MauroMoreyra/EquipoAVL_pcb/TrackerAVL/doc/kicad/Kicad-Multicapa.pdf

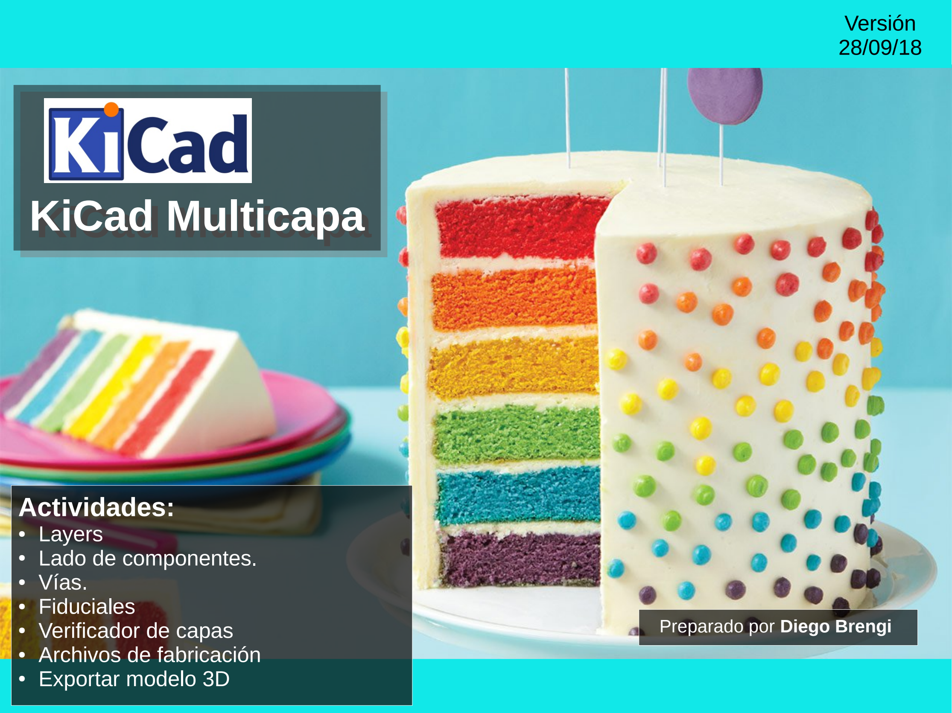
[picture p43: page 1]

# KiCad Multicapa

Preparado por Diego Brengi

Versión
28/09/18

### Actividades:

- Layers
- Lado de componentes.
- Vías.
- Fiduciales
- Verificador de capas
- Archivos de fabricación
- Exportar modelo 3D

Kicad Multicapa – Diego Brengi

Tomaremos el esquemático del ejercicio del oscilador y reharemos el PCB con las siguientes pautas:
- Con componentes SMD.
- Utilizando 4 capas.
- Con componentes de ambos lados.

### Ejercicio Multicapa

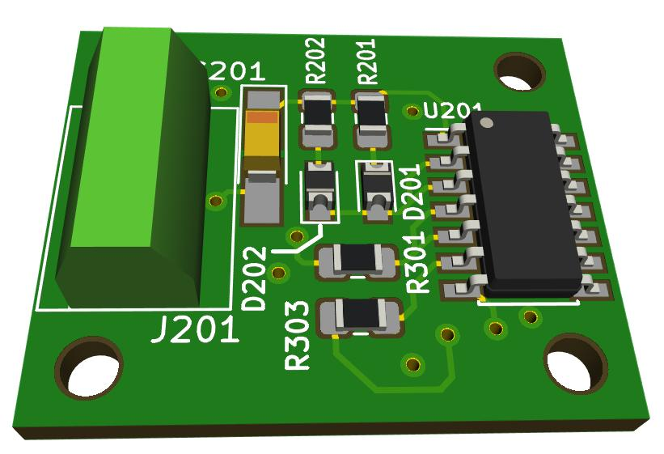
[picture p44: figure]

# CVPCB

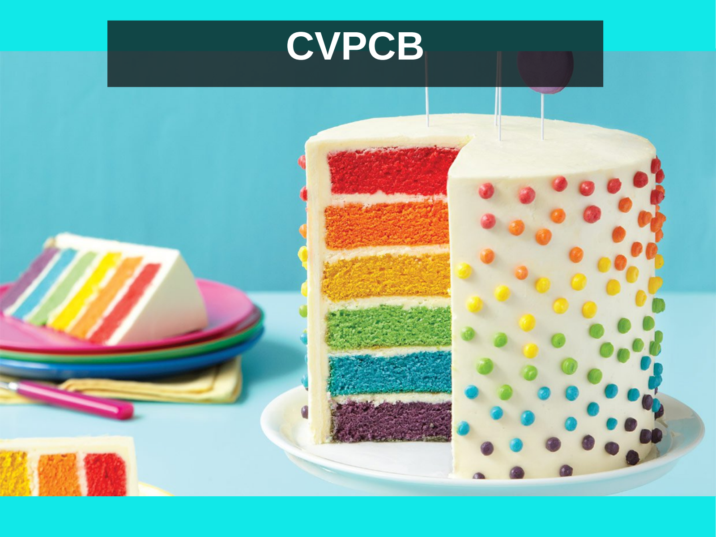
[picture p45: page 3]

Realizamos la asociación de lo componentes, que serán todos SMD salvo la bornera de alimentación.

### Asociación de huellas

Usaremos encapsulados 0805

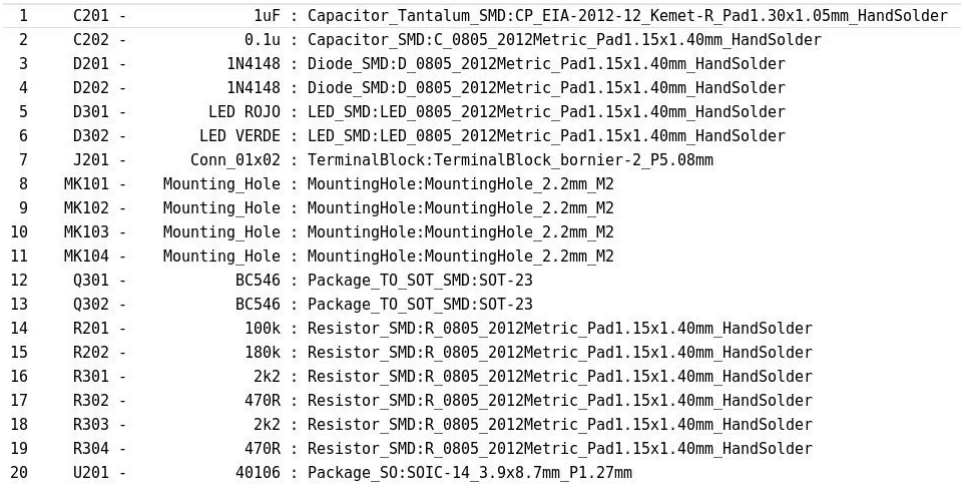
[picture p46: figure]

# PCBNEW

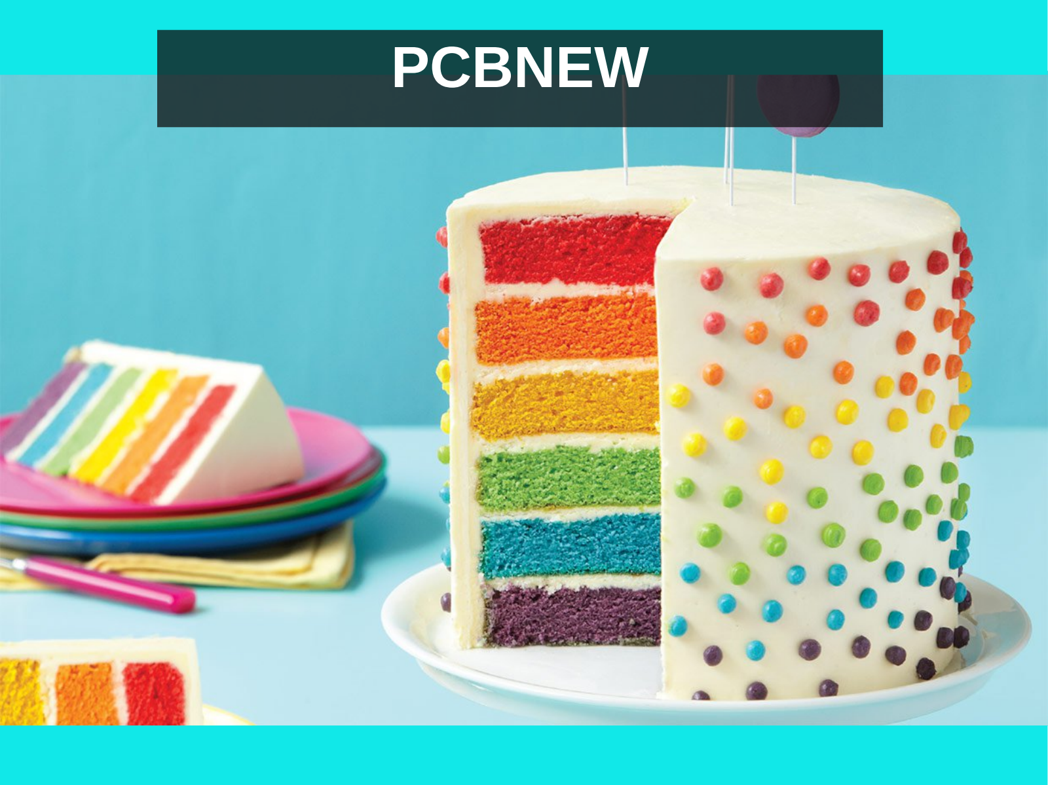
[picture p47: page 5]

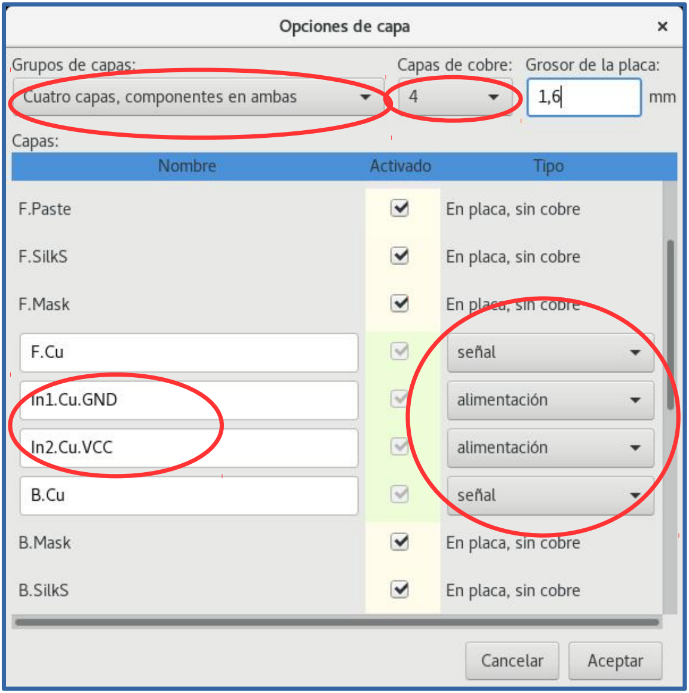
[picture p48: figure]

### Configurar:

- Número de capas.
- Componentes en ambas capas.
- Tipo de capas.
- Nombres de las capas.

### Configurar capas

Utilizaremos un plano completo para GND y otro para VCC.

### Componentes de ambos lados

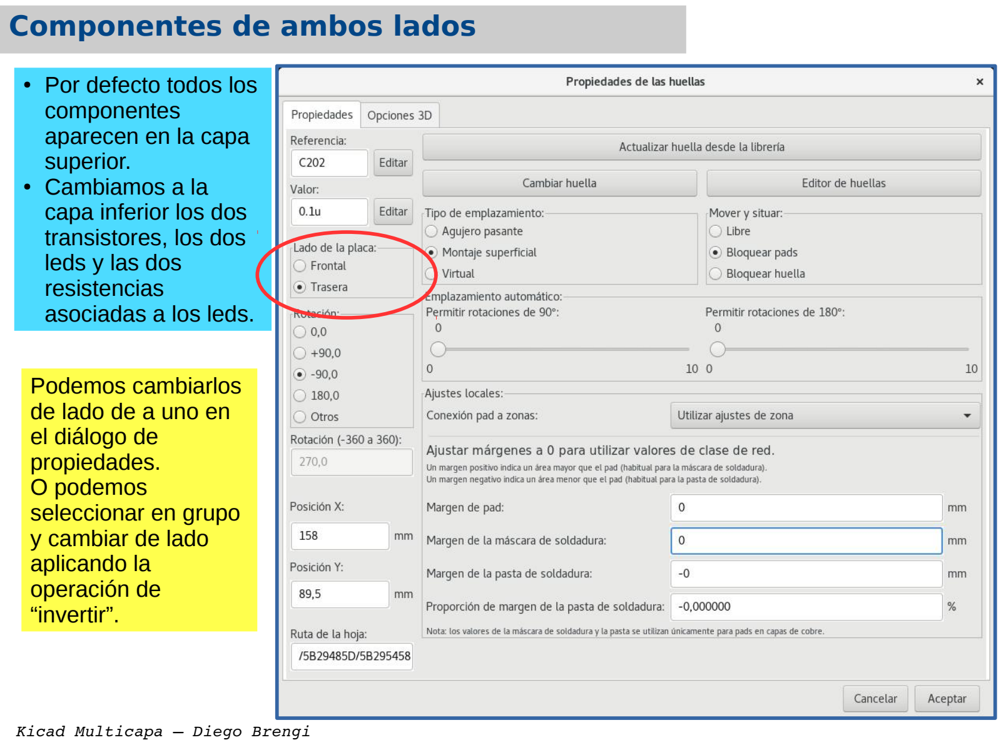
[picture p49: page 7]

- Por defecto todos los
componentes
aparecen en la capa
superior.
- Cambiamos a la
capa inferior los dos
transistores, los dos
leds y las dos
resistencias
asociadas a los leds.

Podemos cambiarlos
de lado de a uno en
el diálogo de
propiedades.
O podemos
seleccionar en grupo
y cambiar de lado
aplicando la
operación de
“invertir”.

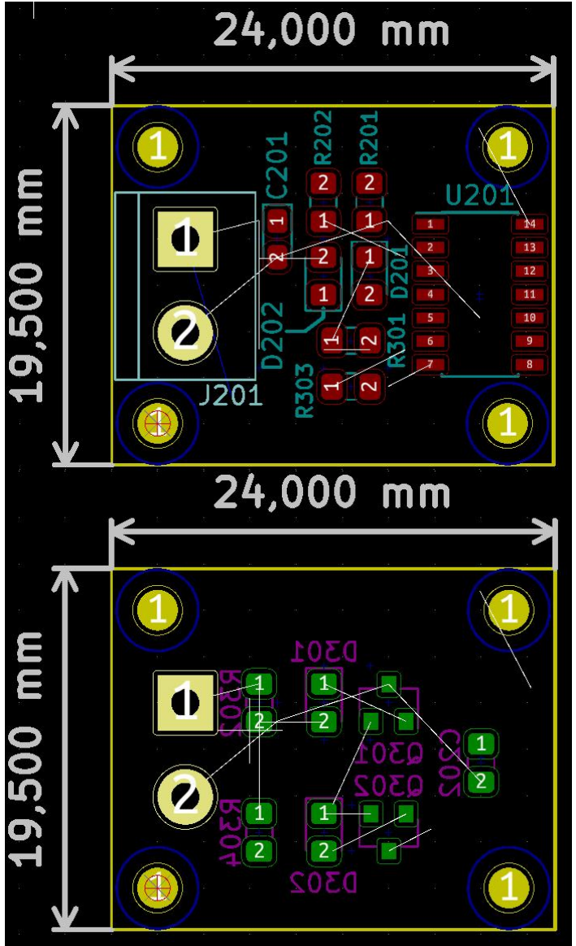
[picture p50: figure]

- Colocar una grilla adecuada.
- Se recomienda 0,5 mm o 0,25 mm.

### Grilla, borde, y ubicación

- Trazar el borde de PCB, de aprox. 24X20 mm.
- Ubicar los componentes.

Tomar las pautas de 10 mils de Mayer:
- Configurar vías: 1mm/0,5mm
- Configurar márgen: 0,25 mm
- Mínima pista: 0,25 mm
- Distancia al borde: 0,3 mm.

- Dibujar los rellenos de cobre, usando toda la capa 2 para GND y toda la 3 para VCC (+5V).

### Planos internos (GND y VCC)

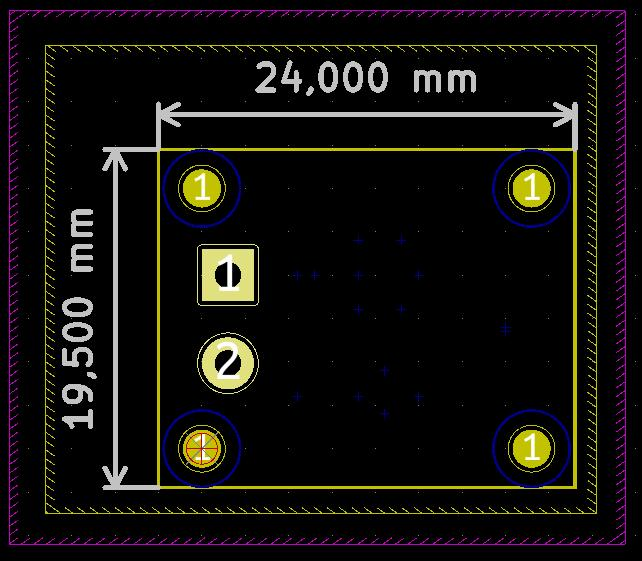
[picture p51: figure]

- Si ya estamos seguros de la ubicación de los componentes, podemos
conectar las alimentaciones a sus correspondientes planos.
Conexiónes de alimentación | La conexión se realizará con una pista corta y una vía.

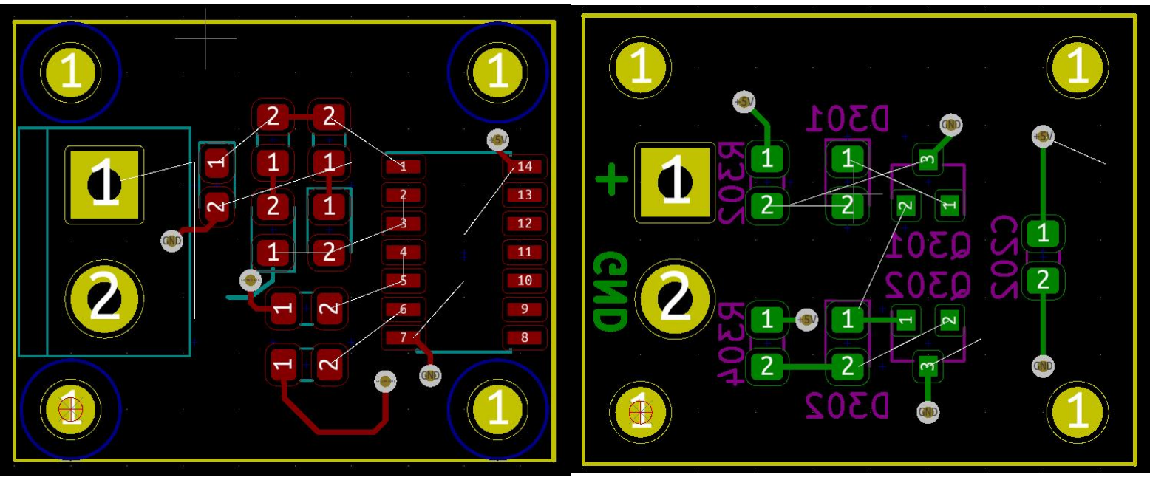
[picture p52: figure]

- Rutear el resto de las conexiones, en capa superior e inferior según corresponda.

### Ruteo de señal

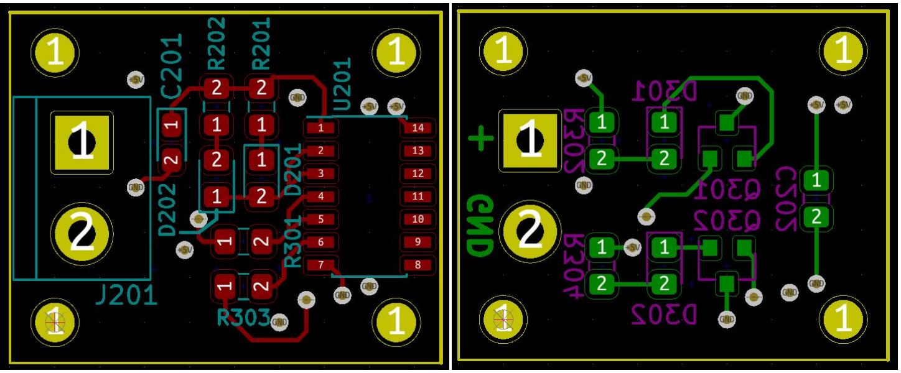
[picture p53: figure]

- Acomodamos las referencias en la serigrafía.
- Agregamos textos en la serigrafía de ambas caras.
- Agregamos IND. ARG. O INDUSTRIA ARGENTINA en alguna capa exterior de cobre.
- Al texto de IND. ARG le quitamos la máscara antisoldante.

### Serigrafía

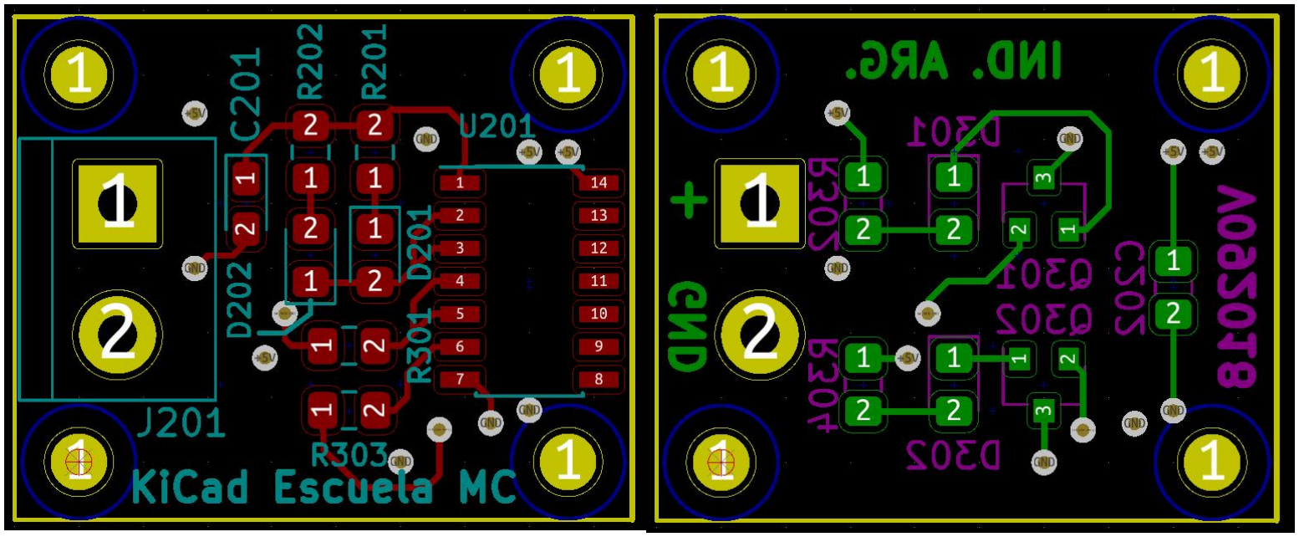
[picture p54: figure]

Agregamos un fiducial en cada capa, aunque lo ideal sería agregar dos o tres por capa para facilitar la tarea del armador.

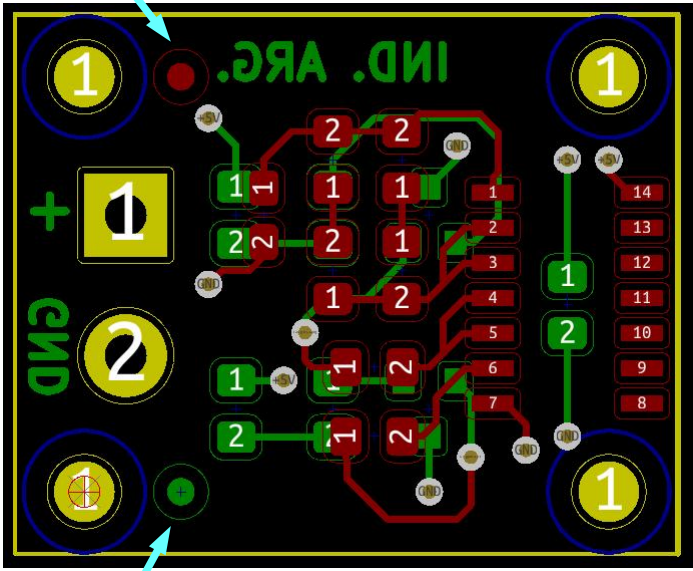
[picture p55: figure]

- Lo hacemos desde el
esquemático.
- Si no encontramos un
símbolo para el Fiducial
podemos usar el símbolo de Mounting Hole, renombrando la referencia a Fx (F1 y F2).
- Luego le asignamos con
CVPCB un fiducial de 1mm
de diámetro interno y 2 mm de diámetro externo.
- En el editor de PCB,
colocamos un fiducial en la capa de cobre superior y el otro en la capa de cobre
inferior.

### Fiduciales

### Verificador de capas

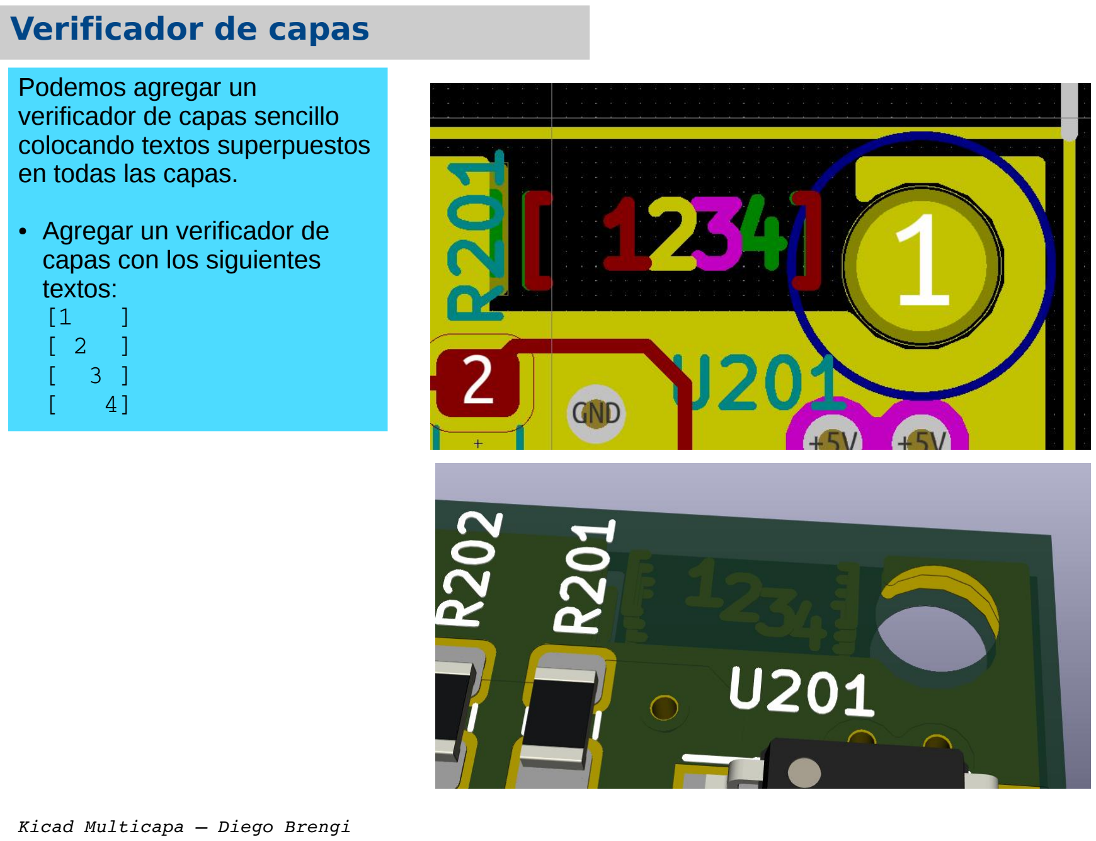
[picture p56: page 14]

Podemos agregar un
verificador de capas sencillo colocando textos superpuestos en todas las capas.
- Agregar un verificador de capas con los siguientes
textos:
[1 ]
[ 2 ]
[ 3 ]
[ 4]

- Realizar Chequeo de DRC y Listado de no conectados.
- Visualizar el modelo 3D.
- Completar los modelos 3D faltantes.
- Verificar serigrafía, fiduciales, textos, etc. observando la vista 3D.

### Chequeo DRC y vista 3D

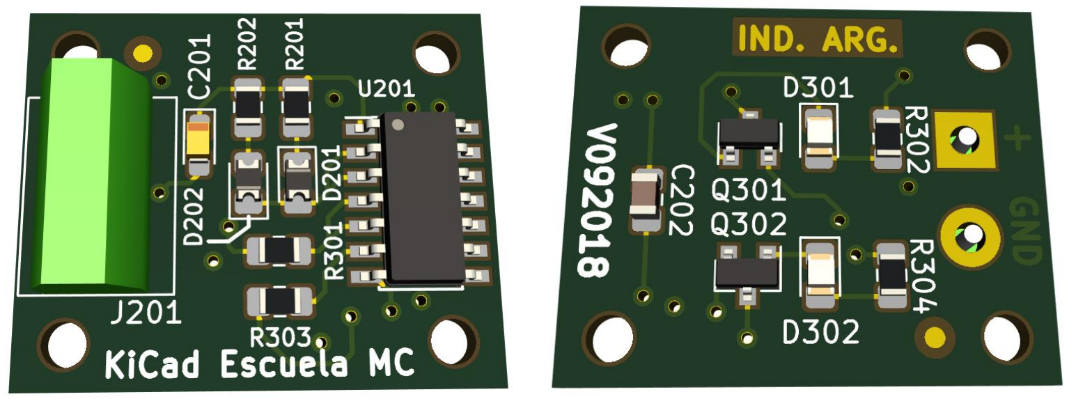
[picture p57: figure]

- Colocar cotas.
- Documentar en la capa Dwgs.user las grillas, márgenes, anchos de pista, terminación superficial, etc.
- Colocar el origen de taladrado, posicionamiento y grilla en el centro del fiducial inferior izquierdo.

### Documentación para fabricación

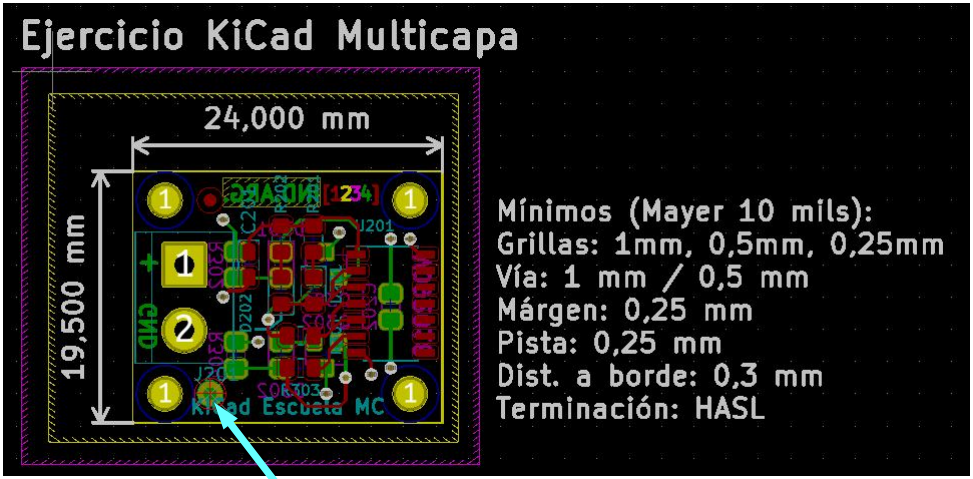
[picture p58: figure]

ORIGEN

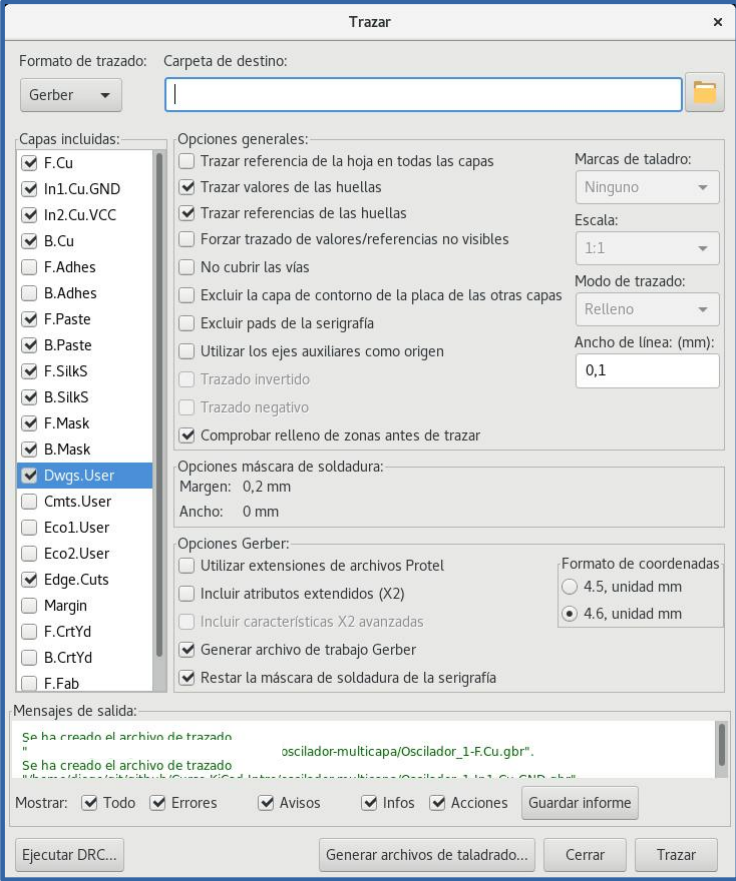
[picture p59: figure]

- Generar los Gerbers y archivo de taladrado: Capas de cobre, serigrafía inferior y superior, máscaras de soldadura superior e inferior, pasta superior e inferior, borde de pcb y anotaciones.

### Documentación para fabricación

Los Gerbers que se manden a fabricar conviene agregarlos al sistema de control de versiones.

### Verificar los gerbers

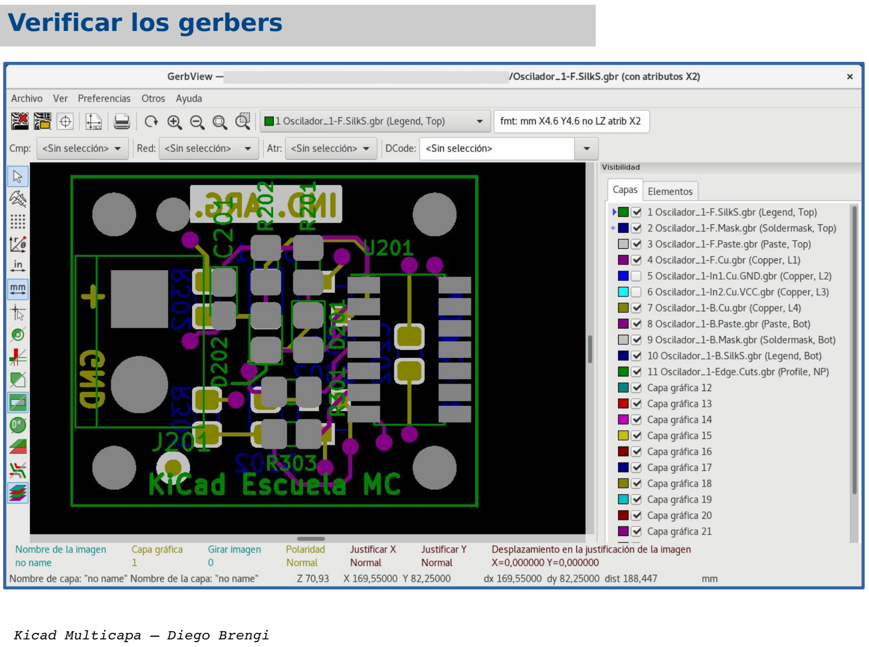
[picture p60: page 18]

- Generar los archivos de posicionamiento, uno por cada lado de componentes.

### Documentación para ensamblaje

### Module positions - created on Wed Sep 26 22:07:47 2018 ###

### Printed by Pcbnew version kicad 5.0.0-fee4fd1~66~ubuntu16.04.1

## Unit = mm, Angle = deg.

## Side : top

# Ref | Val | Package | PosX | PosY | Rot Side

C201 | 1uF | CP_EIA-2012-12_Kemet-R_Pad1.30x1.05mm_HandSolder | 3.0000 | 10.0000 270.0000 top
D201 | 1N4148 | D_0805_2012Metric_Pad1.15x1.40mm_HandSolder | 8.0000 | 8.0000 270.0000 top
D202 | 1N4148 | D_0805_2012Metric_Pad1.15x1.40mm_HandSolder | 5.5000 | 8.0000 | 90.0000 top
R201 | 100k | R_0805_2012Metric_Pad1.15x1.40mm_HandSolder | 8.0000 | 12.0000 | 90.0000 top
R202 | 180k | R_0805_2012Metric_Pad1.15x1.40mm_HandSolder | 5.5000 | 12.0000 | 90.0000 top
R301 | 2k2 | R_0805_2012Metric_Pad1.15x1.40mm_HandSolder | 7.0000 | 4.5000 | 0.0000 top
R303 | 2k2 | R_0805_2012Metric_Pad1.15x1.40mm_HandSolder | 7.0000 | 2.0000 | 0.0000 top
U201 | 40106 | SOIC-14_3.9x8.7mm_P1.27mm | 14.0000 | 7.0000 | 0.0000 top
## End

#### Module positions - created on Wed Sep 26 22:07:47 2018 ### ### Printed by Pcbnew version kicad 5.0.0-fee4fd1~66~ubuntu16.04.1

## Unit = mm, Angle = deg.

## Side : bottom

# Ref | Val | Package | PosX | PosY | Rot Side

C202 | 0.1u | C_0805_2012Metric_Pad1.15x1.40mm_HandSolder | -14.0000 | 6.7500 270.0000 bottom
D301 | LED_ROJO | LED_0805_2012Metric_Pad1.15x1.40mm_HandSolder | -5.5000 | 10.0000 270.0000 bottom
D302 | LED_VERDE LED_0805_2012Metric_Pad1.15x1.40mm_HandSolder | -5.5000 | 3.0000 270.0000 bottom
Q301 | BC546 | SOT-23 | -9.0000 | 10.0000 | 90.0000 bottom
Q302 | BC546 | SOT-23 | -9.0000 | 3.0000 270.0000 bottom
R302 | 470R | R_0805_2012Metric_Pad1.15x1.40mm_HandSolder | -2.0000 | 10.0000 270.0000 bottom
R304 | 470R | R_0805_2012Metric_Pad1.15x1.40mm_HandSolder | -2.0000 | 3.0000 270.0000 bottom
## End

### Documentación del diseño

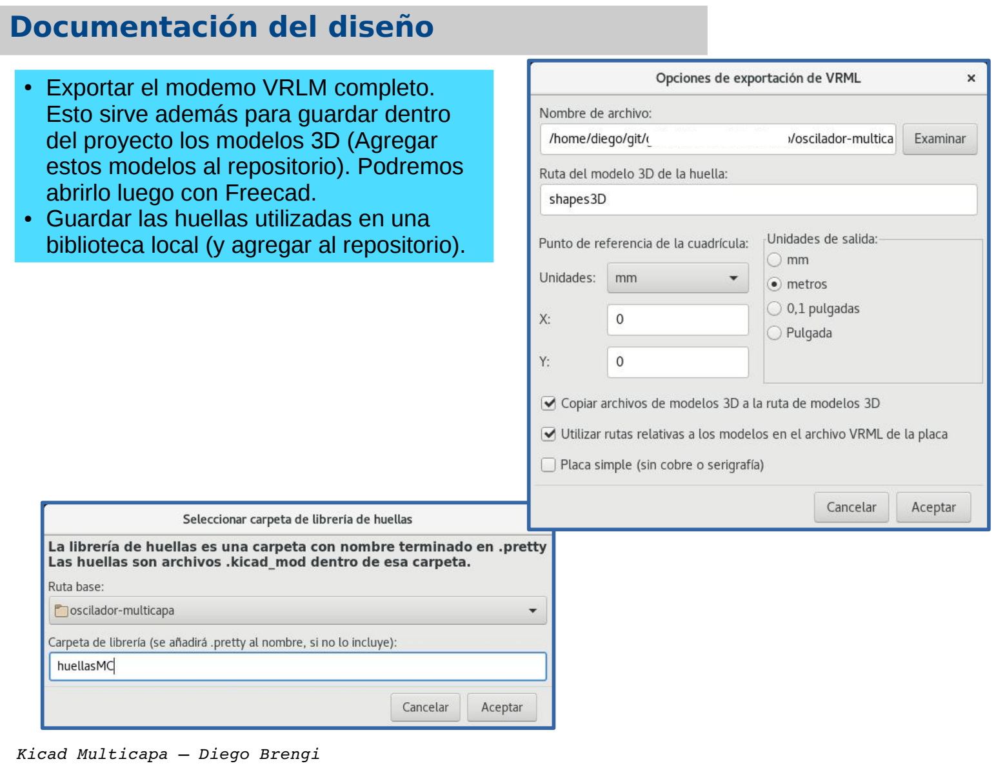
[picture p61: page 20]

- Exportar el modemo VRLM completo. Esto sirve además para guardar dentro del proyecto los modelos 3D (Agregar estos modelos al repositorio). Podremos abrirlo luego con Freecad.
- Guardar las huellas utilizadas en una biblioteca local (y agregar al repositorio).

### Autores e imágenes de esta presentación

Las imágenes de clipart se tomaron de: https://openclipart.org/
Los demás logos corresponden a proyectos de Software Libre u Open Source. Consultar cada licencia en particular.
Todas las capturas de pantalla fueron realizadas por los autores y están bajo la misma licencia que esta presentación.

Carátula principal:
https://parade.com/wp-content/uploads/2014/09/rainbow-layer-cake-ftr.jpg

El resto de las imágenes se cita la fuente debajo de cada una.

Autor de esta presentación y contacto:
Diego Brengi - djavier@ieee.org
“KiCad - Multicapa”
Preparado para la Carrera de Especialización en Sistemas Embebidos del LSE-FIUBA (CESE).
