MauroMoreyra/EquipoAVL_pcb/TrackerAVL/doc/kicad/Kicad_Rejunte.pdf

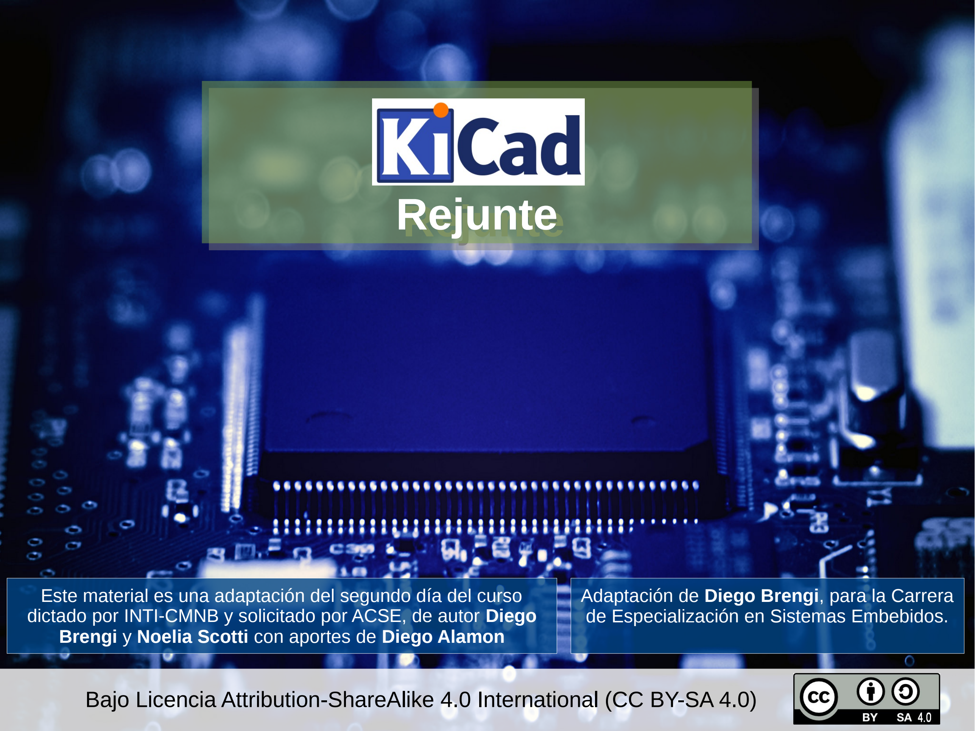
[picture p82: page 1]

Bajo Licencia Attribution-ShareAlike 4.0 International (CC BY-SA 4.0)

# Rejunte

Este material es una adaptación del segundo día del curso dictado por INTI-CMNB y solicitado por ACSE, de autor Diego Brengi y Noelia Scotti con aportes de Diego Alamon

Adaptación de Diego Brengi, para la Carrera de Especialización en Sistemas Embebidos.

# Profundizando en el

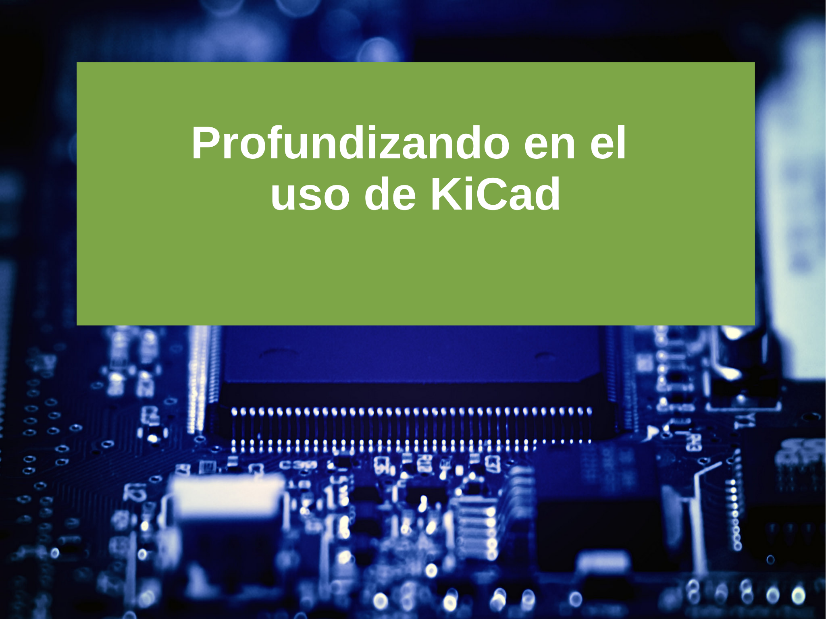
[picture p83: page 2]

# uso de KiCad

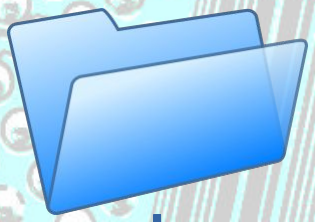
[picture p84: figure]

Curso Kicad – INTI – CMNB – Diego Brengi – Noelia Scotti – Diego Alamon

Nuestro diseño tendrá una estructura de directorios planificada previamente. No hay una regla estricta para esta organización, pero es muy conveniente
tenerla y mantenerla en todos nuestros diseños. Sugerencia:

### Ejercicio 2 – Planificación de directorios

1) Crear la
estructura de
directorios.

Ejercicio2
libs: Biblioteca de símbolos de nuestro diseño. ej2.pretty: Footprints.
ej2.3dshapes: Modelos 3D.
tools: Herramientas complementarias. gerber: Archivos gerber.
doc: Documentación y licencia. datasheets: Hojas de datos relevantes.

### Eeschema – Buses

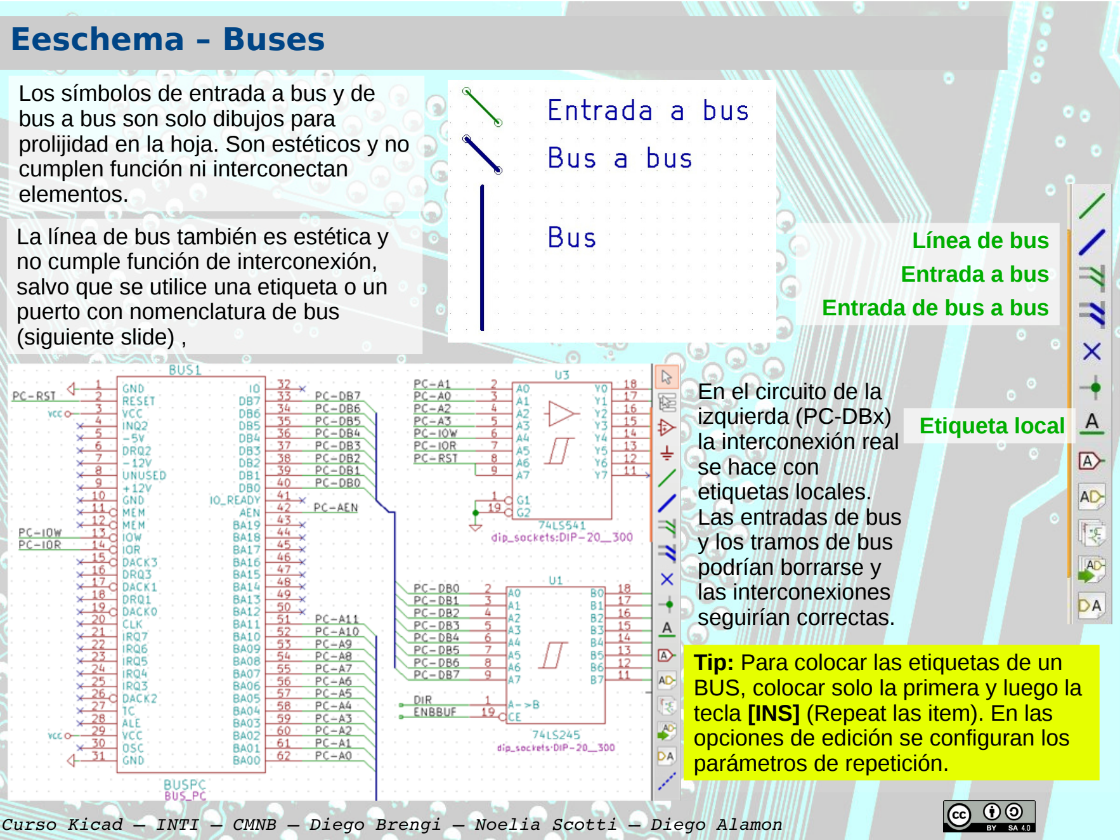
[picture p85: page 4]

Los símbolos de entrada a bus y de bus a bus son solo dibujos para prolijidad en la hoja. Son estéticos y no cumplen función ni interconectan elementos.

Línea de bus
Entrada a bus
Entrada de bus a bus

Etiqueta local

La línea de bus también es estética y no cumple función de interconexión, salvo que se utilice una etiqueta o un puerto con nomenclatura de bus (siguiente slide) ,

En el circuito de la
izquierda (PC-DBx)
la interconexión real
se hace con
etiquetas locales.
Las entradas de bus
y los tramos de bus
podrían borrarse y
las interconexiones
seguirían correctas.

Tip: Para colocar las etiquetas de un BUS, colocar solo la primera y luego la tecla [INS] (Repeat las item). En las opciones de edición se configuran los parámetros de repetición.

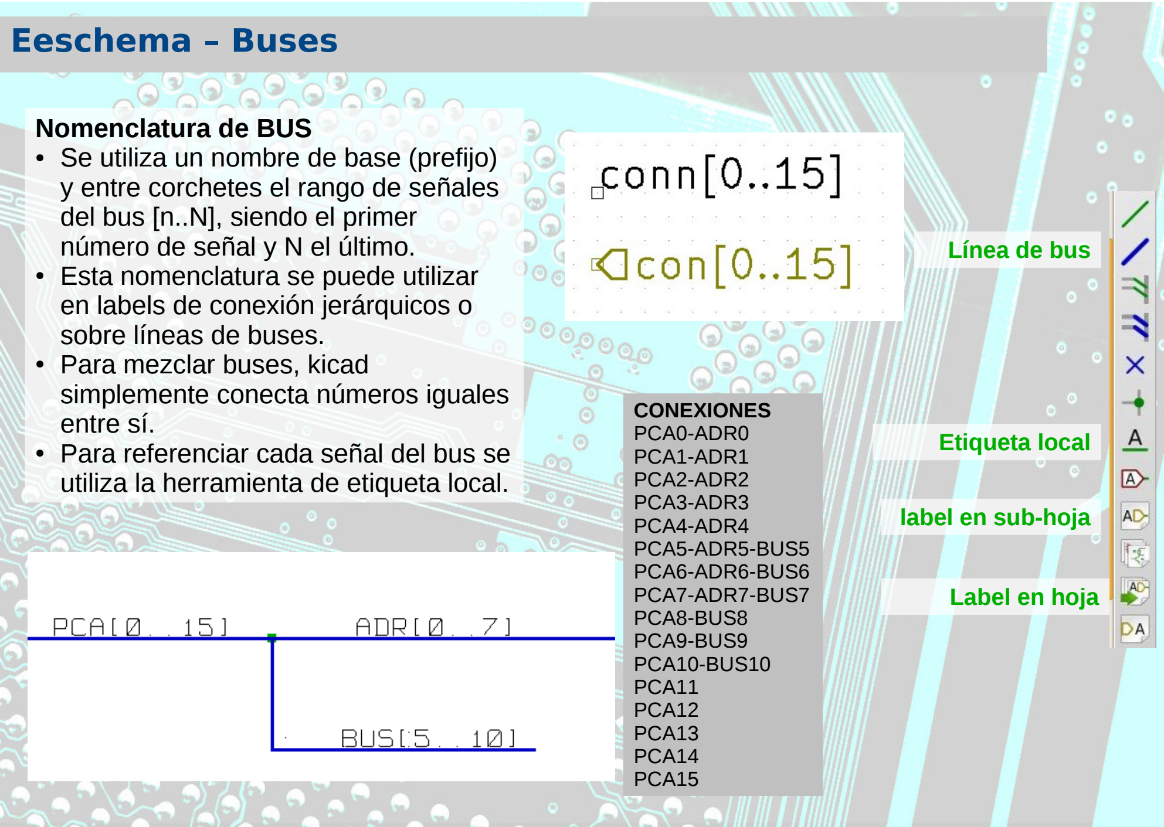
[picture p86: figure]
Eeschema – Buses; Línea de bus; Nomenclatura de BUS; y entre corchetes el rango de señales del bus [n..N], siendo el primer número de señal y N el último. ● Esta nomenclatura se puede utilizar en labels de conexión jerárquicos o sobre líneas de buses. ● Para mezclar buses, kicad simplemente conecta números iguales entre sí.; Etiqueta local; label en sub-hoja; Label en hoja; CONEXIONES PCA0-ADR0 PCA1-ADR1 PCA2-ADR2 PCA3-ADR3 PCA4-ADR4 PCA5-ADR5-BUS5 PCA6-ADR6-BUS6 PCA7-ADR7-BUS7 PCA8-BUS8 PCA9-BUS9 PCA10-BUS10 PCA11 PCA12 PCA13 PCA14 PCA15

- Se utiliza un nombre de base (prefijo)
- Para referenciar cada señal del bus se utiliza la herramienta de etiqueta local.

### Eeschema – Jerarquía de hojas y buses

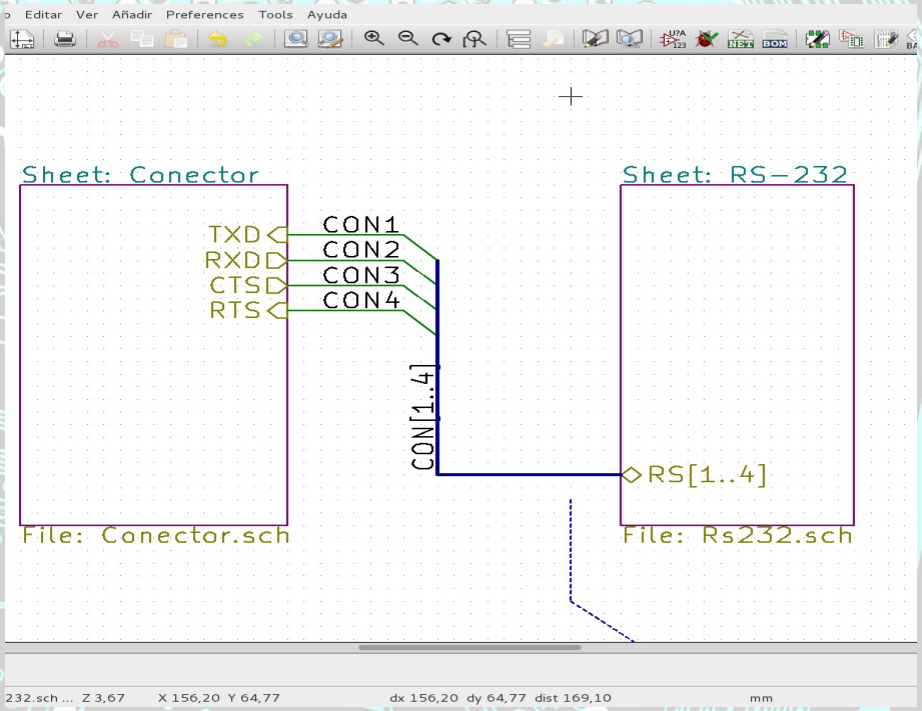
[picture p87: figure]

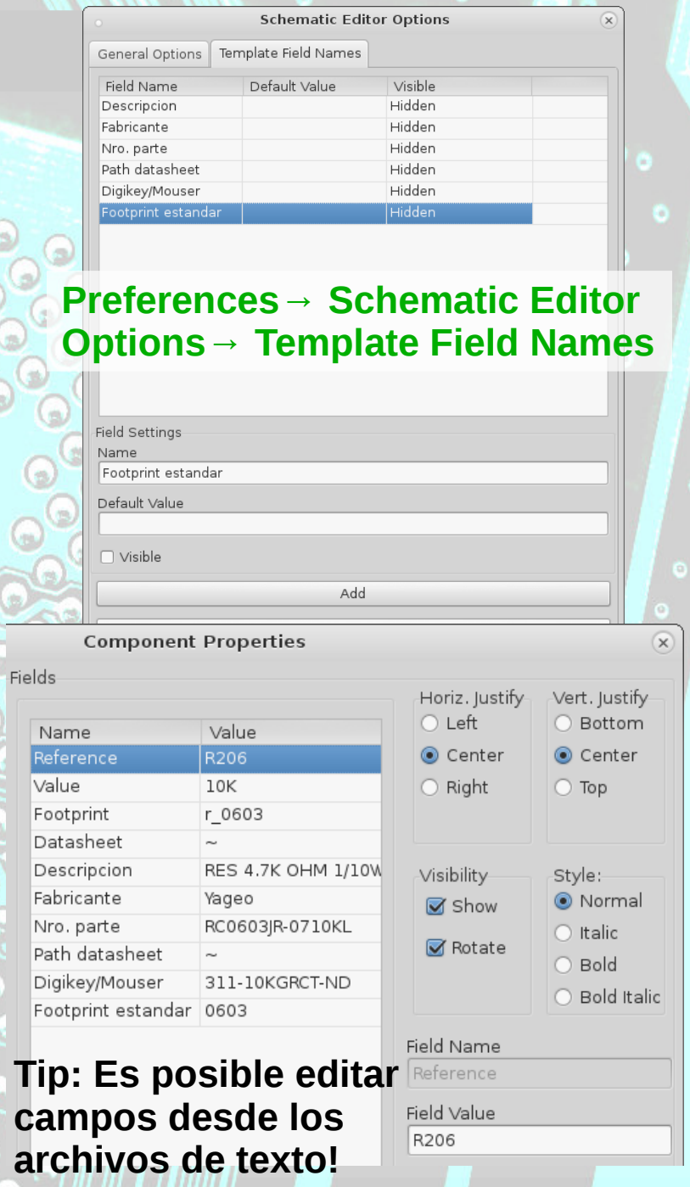
[picture p88: figure]
Preferences→ Schematic Editor Options→ Template Field Names; Tip: Es posible editar campos desde los archivos de texto!

Campos de información: Por qué se usan?

- Correcta identificación de cada componente desde el momento que el desarrollador lo agrega al esquemático.
- Uniformidad de la descripción de todos los componentes.
- Obtención de una lista de componentes completa y ordenada para realizar la compra de materiales.

### Eeschema – Campos de Información

Campos de información: Cómo se usan?

1) Acordar con todos los desarrolladores los campos que se utilizarán y cómo se completarán.
2) Chequear que todos tengan los campos escritos exactamente igual, no es lo mismo NRO. DE PARTE que NÚMERO DE PARTE!
3) Completar los campos a medida que se van agregando los componentes al esquemático, no dejar para el final.
4) No cambiar ni agregar campos durante el transcurso del proyecto para no generar conflictos.

### Eeschema – Campos de información

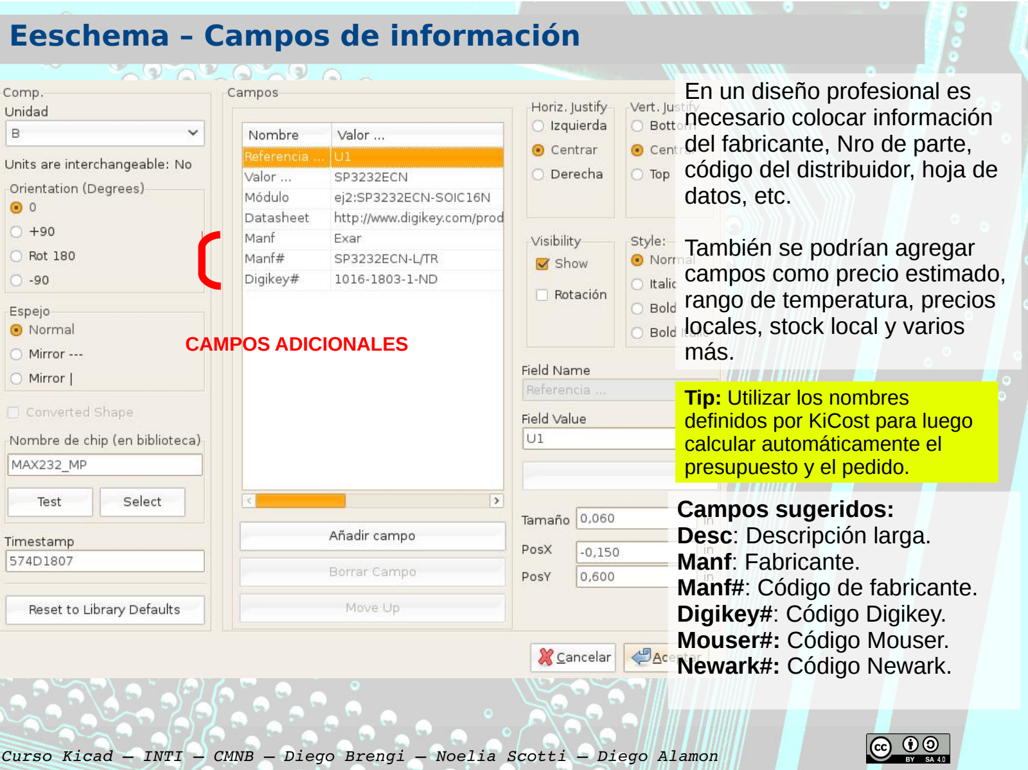
[picture p89: page 8]

En un diseño profesional es necesario colocar información del fabricante, Nro de parte, código del distribuidor, hoja de datos, etc.

También se podrían agregar campos como precio estimado, rango de temperatura, precios locales, stock local y varios
más. CAMPOS ADICIONALES

Campos sugeridos:
Desc: Descripción larga.
Manf: Fabricante.
Manf#: Código de fabricante. Digikey#: Código Digikey.
Mouser#: Código Mouser.
Newark#: Código Newark.

Tip: Utilizar los nombres
definidos por KiCost para luego calcular automáticamente el presupuesto y el pedido.

### BOM – Listado de materiales

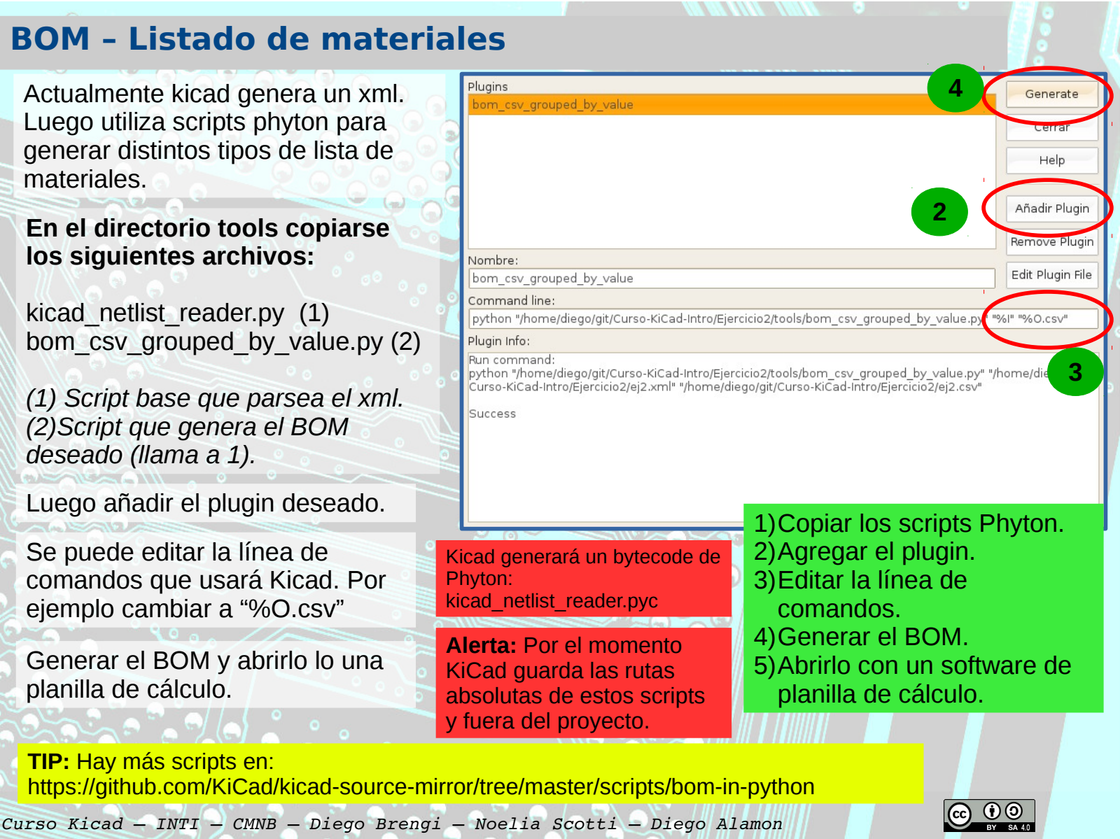
[picture p90: page 9]

Actualmente kicad genera un xml. Luego utiliza scripts phyton para generar distintos tipos de lista de materiales.

Luego añadir el plugin deseado. Se puede editar la línea de comandos que usará Kicad. Por ejemplo cambiar a “%O.csv”

2

3

Generar el BOM y abrirlo lo una planilla de cálculo.

1)Copiar los scripts Phyton. 2)Agregar el plugin.
3)Editar la línea de
comandos.
4)Generar el BOM.
5)Abrirlo con un software de planilla de cálculo.

4

TIP: Hay más scripts en:
https://github.com/KiCad/kicad-source-mirror/tree/master/scripts/bom-in-python

Alerta: Por el momento
KiCad guarda las rutas
absolutas de estos scripts y fuera del proyecto.

En el directorio tools copiarse los siguientes archivos:

kicad_netlist_reader.py (1) bom_csv_grouped_by_value.py (2)

(1) Script base que parsea el xml. (2)Script que genera el BOM deseado (llama a 1).

Kicad generará un bytecode de Phyton:
kicad_netlist_reader.pyc

Vamos a realizar un footprint SMD para soldar a mano un 1206. Los pads son un poco más grandes que el 1206 normal.

### Ejercicio 2 – Creación de footprints

1)Abrir el editor de módulos. 2)Nuevo footprint.

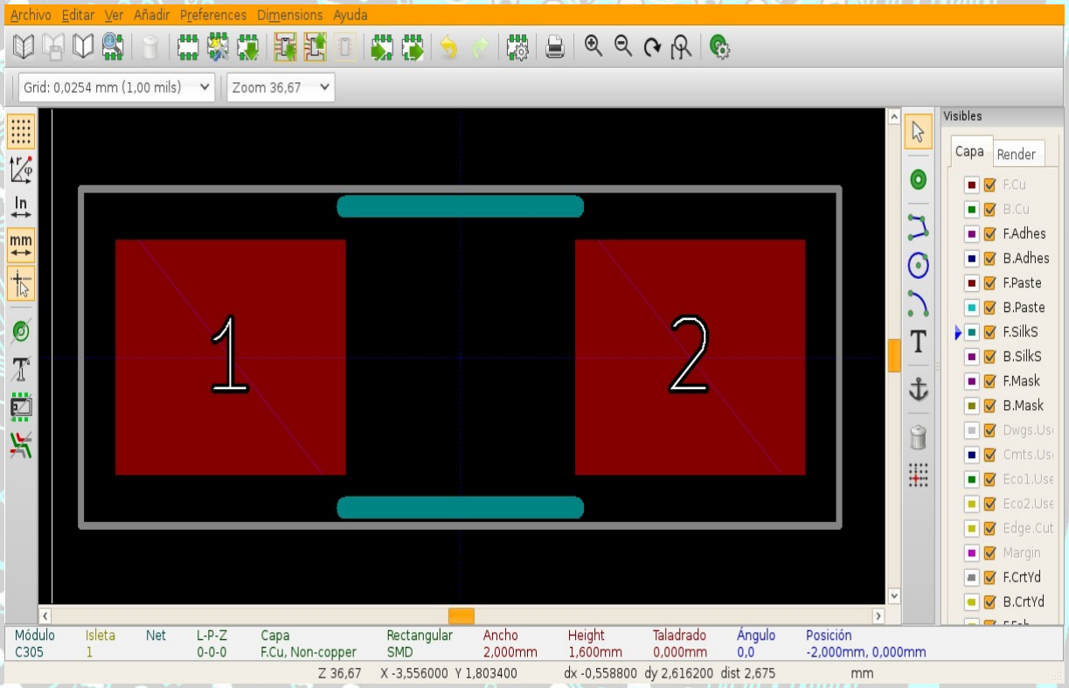
[picture p91: figure]

### Ejercicio 2 – Creación de footprints

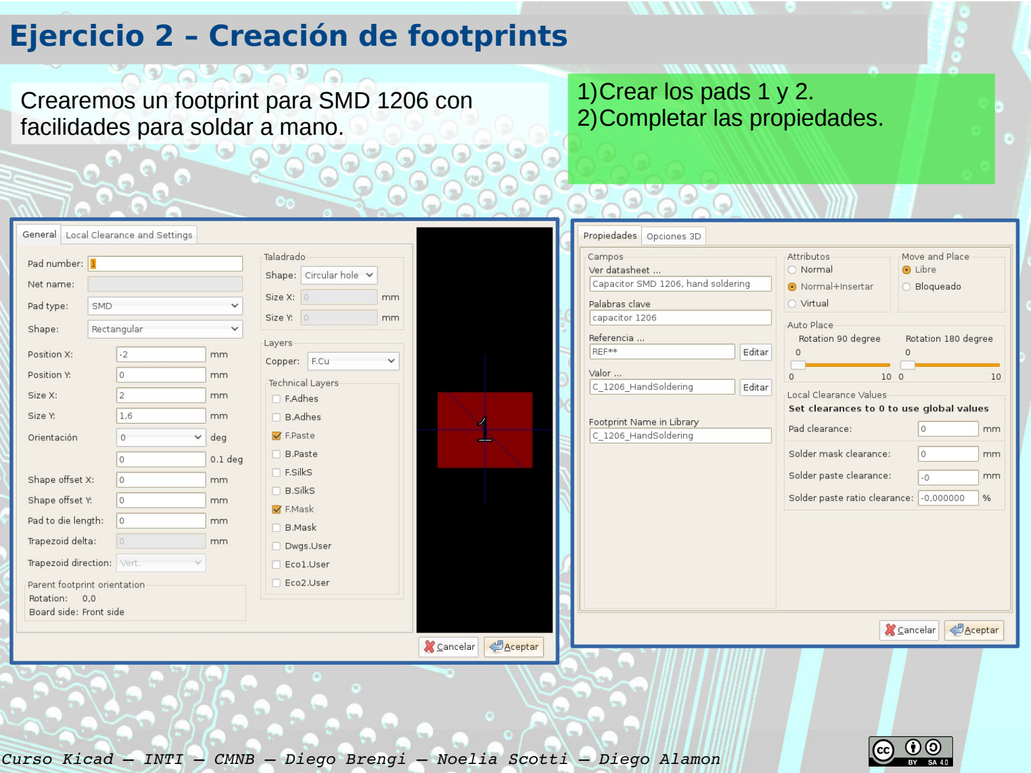
[picture p92: page 11]

Crearemos un footprint para SMD 1206 con facilidades para soldar a mano.

1)Crear los pads 1 y 2.
2)Completar las propiedades.

### Ejercicio 2 – Creación de footprints

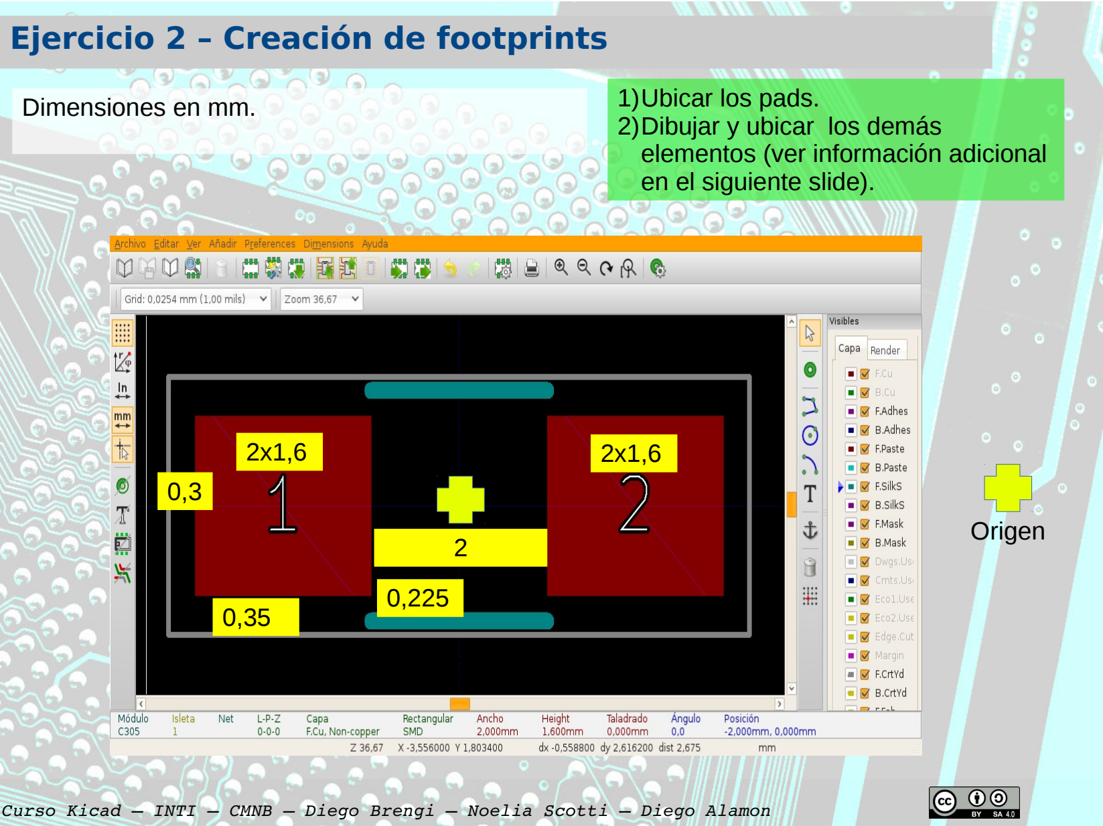
[picture p93: page 12]

Dimensiones en mm.

1)Ubicar los pads.
2)Dibujar y ubicar los demás elementos (ver información adicional en el siguiente slide).

2x1,6

2

0,225
0,35

0,3

2x1,6

Origen

### Ejercicio 2 – Creación de footprints

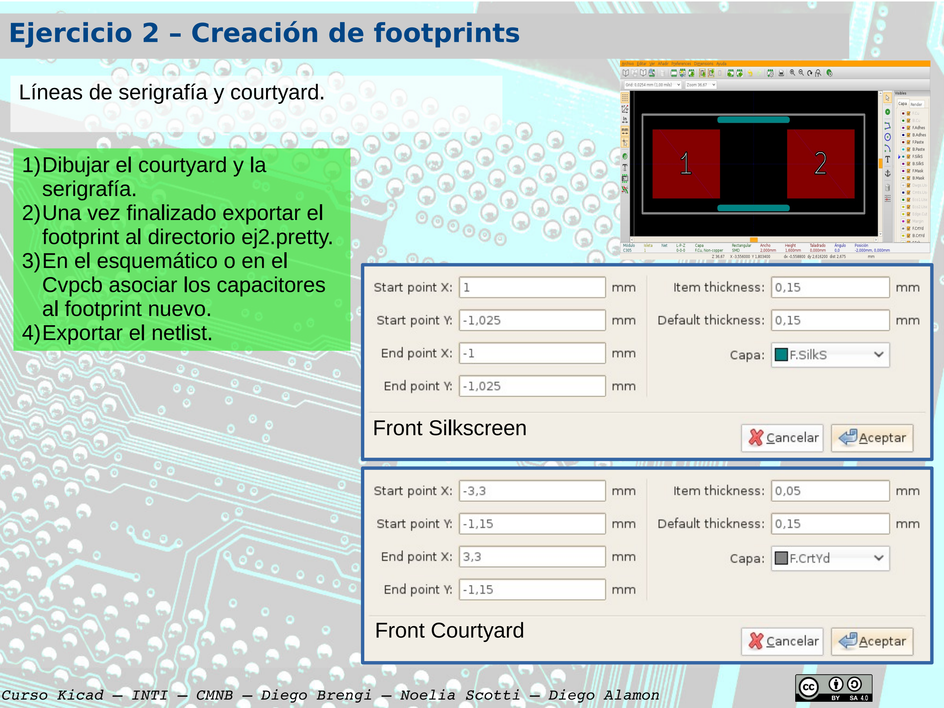
[picture p94: page 13]

Líneas de serigrafía y courtyard.

1)Dibujar el courtyard y la serigrafía.
2)Una vez finalizado exportar el footprint al directorio ej2.pretty. 3)En el esquemático o en el Cvpcb asociar los capacitores al footprint nuevo.
4)Exportar el netlist.

Front Courtyard

Front Silkscreen

### Verificaciones

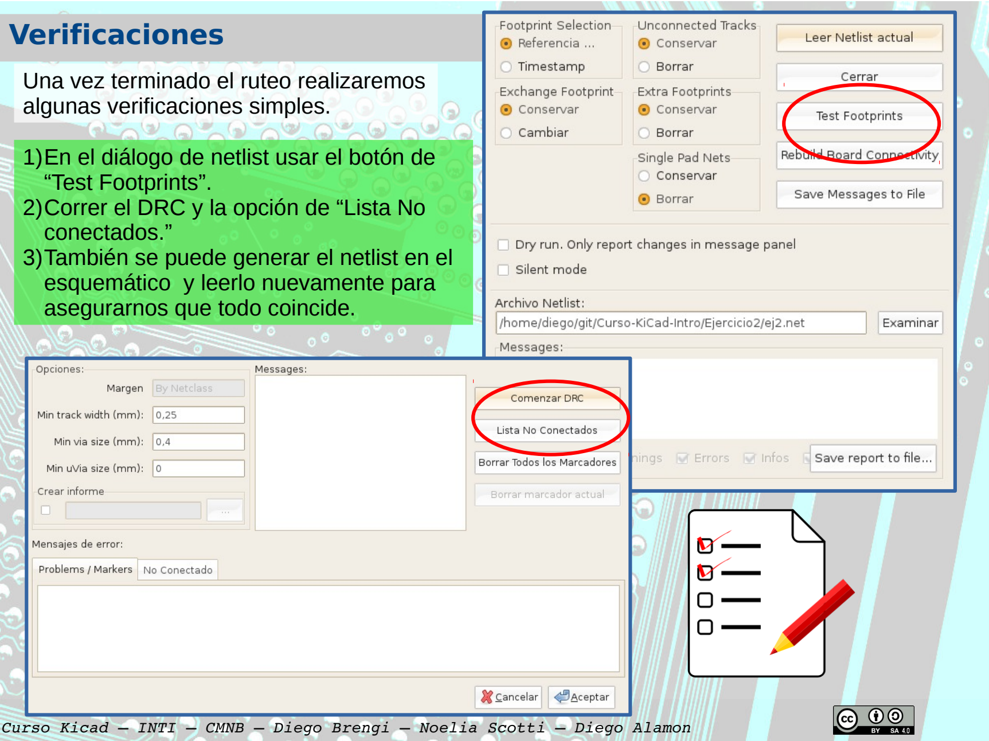
[picture p95: page 14]

1)En el diálogo de netlist usar el botón de “Test Footprints”.
2)Correr el DRC y la opción de “Lista No conectados.”
3)También se puede generar el netlist en el esquemático y leerlo nuevamente para asegurarnos que todo coincide.

Una vez terminado el ruteo realizaremos algunas verificaciones simples.

### Taladrado: Reporte y mapa

Además de los archivos gerbers, se debe revisar el
reporte de taladrado para saber los distintos agujeros
que tenemos. Podríamos optimizar si es necesario. | Drill report for CIAA_K60.kicad_pcb
| Created on mar 01 dic 2015 22:25:47 ART
| Drill report for plated through holes :
| T1 0,41mm 0,016" (456 holes)
| T2 0,75mm 0,030" (4 holes)
| T3 0,90mm 0,035" (8 holes)
| T4 1,00mm 0,039" (20 holes)
| T5 1,02mm 0,040" (88 holes)
| T6 1,20mm 0,047" (8 holes)
| T7 1,40mm 0,055" (40 holes)
| T8 1,50mm 0,059" (10 holes)
| T9 1,60mm 0,063" (2 holes)
| T10 3,40mm 0,134" (2 holes)
| T11 4,00mm 0,157" (4 holes)
| Total plated holes count 642
| Drill report for buried and blind vias :
| Holes from layer TOP to layer GND :
| Total plated holes count 0
| Holes from layer GND to layer PWR :
| Total plated holes count 0
| Holes from layer PWR to layer BOT :
| Total plated holes count 0
| Drill report for unplated through holes :
| T1 3,25mm 0,128" (2 holes)
| Total unplated holes count 2

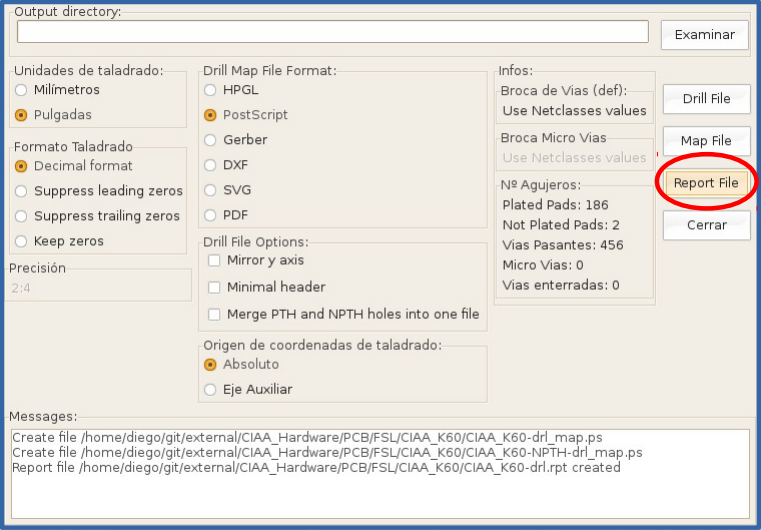
[picture p96: figure]

### Taladrado: Reporte y mapa

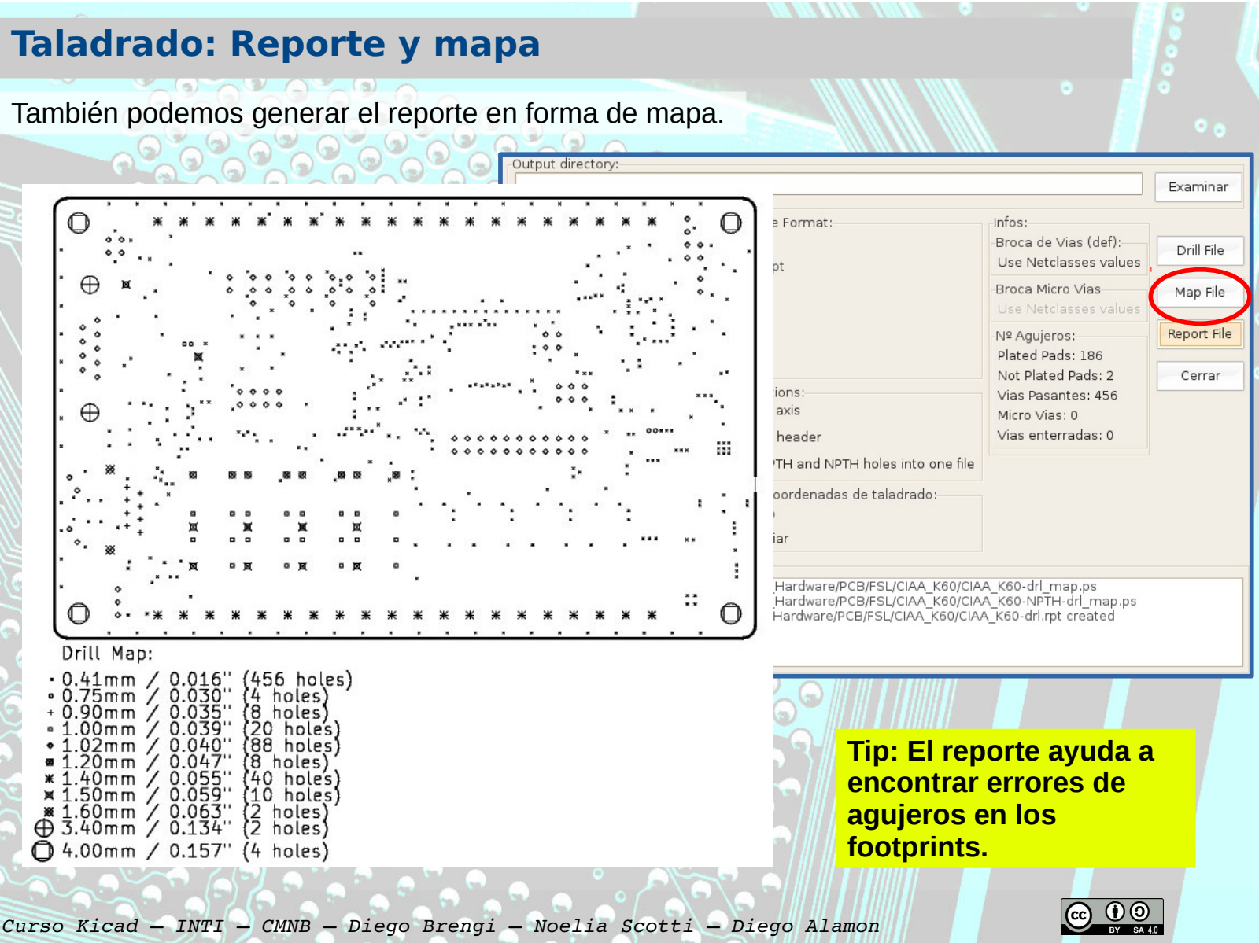
[picture p97: page 16]

También podemos generar el reporte en forma de mapa.

Tip: El reporte ayuda a
encontrar errores de
agujeros en los
footprints.

Modelos 3D: Cuándo usarlos?
- Cuando se va a diseñar un gabinete o se necesita

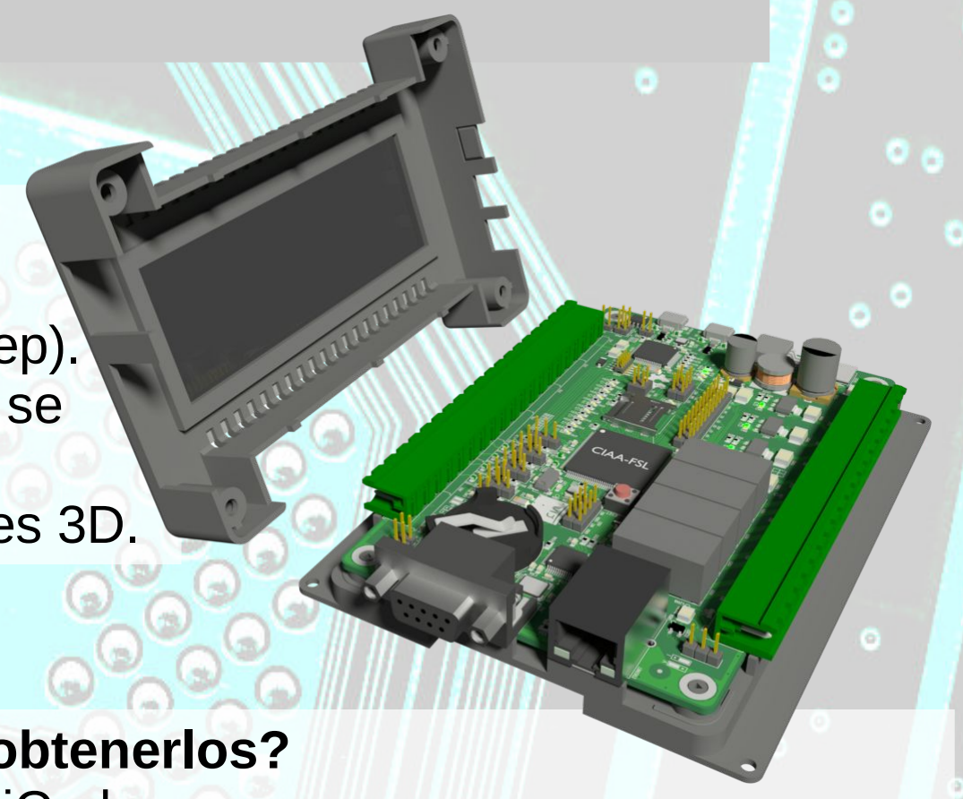
[picture p98: figure]

chequear uno existente (se debe tener el modelo step).
- Cuando se quiere verificar que los componentes no se toquen entre sí o no tapen la serigrafía.
- Para promocionar un producto o realizar animaciones 3D.

### Pcbnew – Modelos 3D I

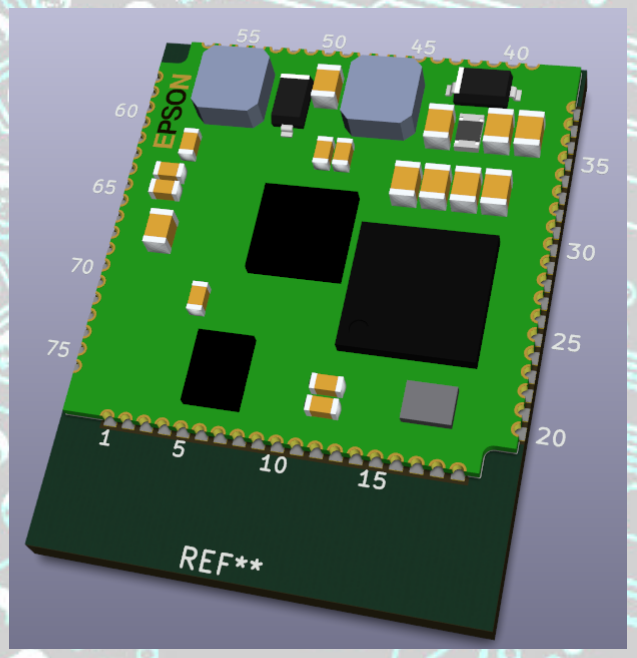
[picture p99: figure]

Modelos 3D: De dónde obtenerlos?
- Librerías estándar de KiCad
https://github.com/KiCad/kicad-library/tree/master/modules/packages3d
también en (/usr/local/share/kicad/modules/packages3d).
- Bajar el modelo IGES o STEP que provea el fabricante y convertirlo al formato VRML (.WRL) con FreeCad.
- Bajar el modelo de la página www.3dcontentcentral.com (ver licencias).
- Crear el modelo 3D con FreeCad.
Tip: Usar FreeCad para
convertir archivos o
superponer modelos 3D.

### Pcbnew – Modelos 3D II

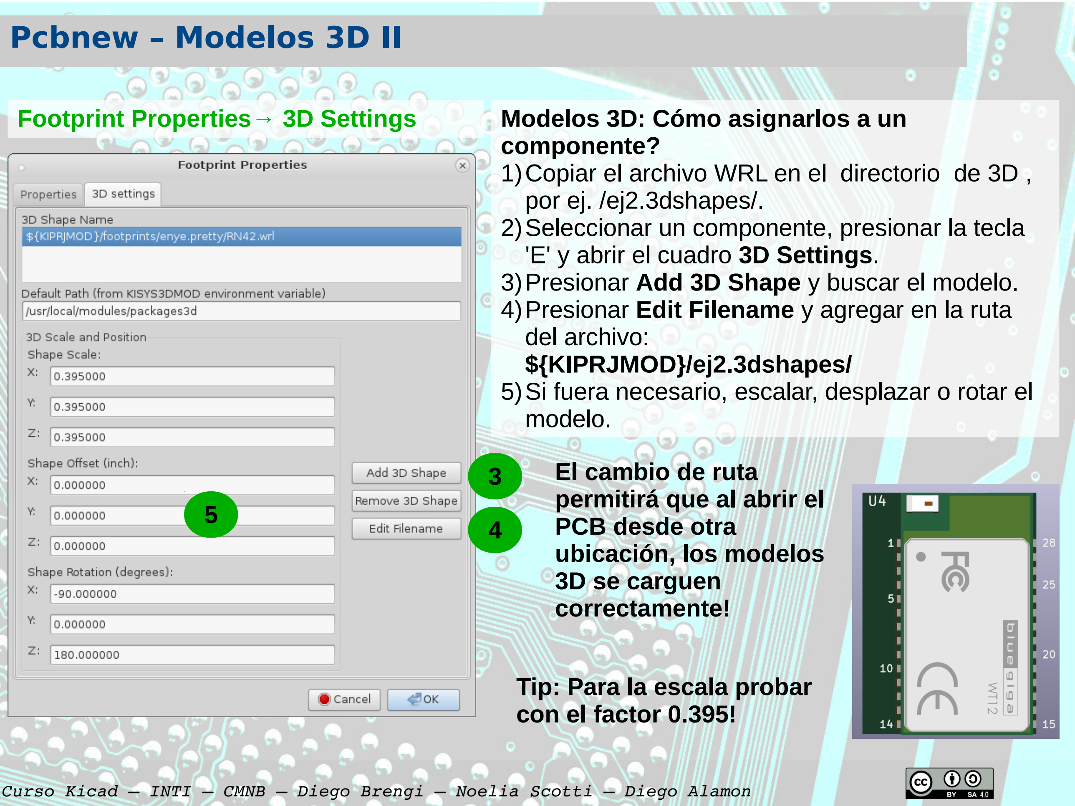
[picture p100: page 18]

Modelos 3D: Cómo asignarlos a un componente?
1)Copiar el archivo WRL en el directorio de 3D , por ej. /ej2.3dshapes/.
2)Seleccionar un componente, presionar la tecla 'E' y abrir el cuadro 3D Settings.
3)Presionar Add 3D Shape y buscar el modelo. 4)Presionar Edit Filename y agregar en la ruta del archivo:
${KIPRJMOD}/ej2.3dshapes/
5)Si fuera necesario, escalar, desplazar o rotar el modelo.

3

4

5

Footprint Properties→ 3D Settings

El cambio de ruta
permitirá que al abrir el
PCB desde otra
ubicación, los modelos
3D se carguen
correctamente!

Tip: Para la escala probar con el factor 0.395!

### Autores e imágenes de esta presentación

Las imágenes de clipart se tomaron de: https://openclipart.org/
Los demás logos corresponden a proyectos de Software Libre u Open Source. Consultar cada licencia en particular.
Todas las capturas de pantalla fueron realizadas por los autores y están bajo la misma licencia que esta presentación.

Carátula principal:
Foto titulada “Circuit” de Yuri Samoilov bajo licencia CC-BY disponible en https://www.flickr.com/photos/yusamoilov/14011462899/
Fondo de la presentación:
Foto titulada “computer motherboard tracks” de Creativity103 bajo licencia CC-BY disponible en: https://www.flickr.com/photos/creative_stock/5228433146/

El resto de las imágenes se cita la fuente debajo de cada una.

Las imágenes del circuito esquemático con un BUS y la interconexión de tres BUSES fueron obtenidas del manual de KiCad http://docs.kicad-pcb.org/en/eeschema.html que pose licencia CC BY 3.0.

Versión - 13/06/16
Autor de esta adaptación y contacto:
Diego Brengi - djavier@ieee.org
“Escuela KiCad - Curso de diseño de circuitos impresos”
Preparado para la Carrera de Especialización en Sistemas Embebidos del LSE-FIUBA (CESE)
